Troelsbk/3d-printed-line-follower-robot-stm32/KiCad/KiCad.kicad_sch

## KiCad design KiCad/KiCad.kicad_sch (2025-11-29)

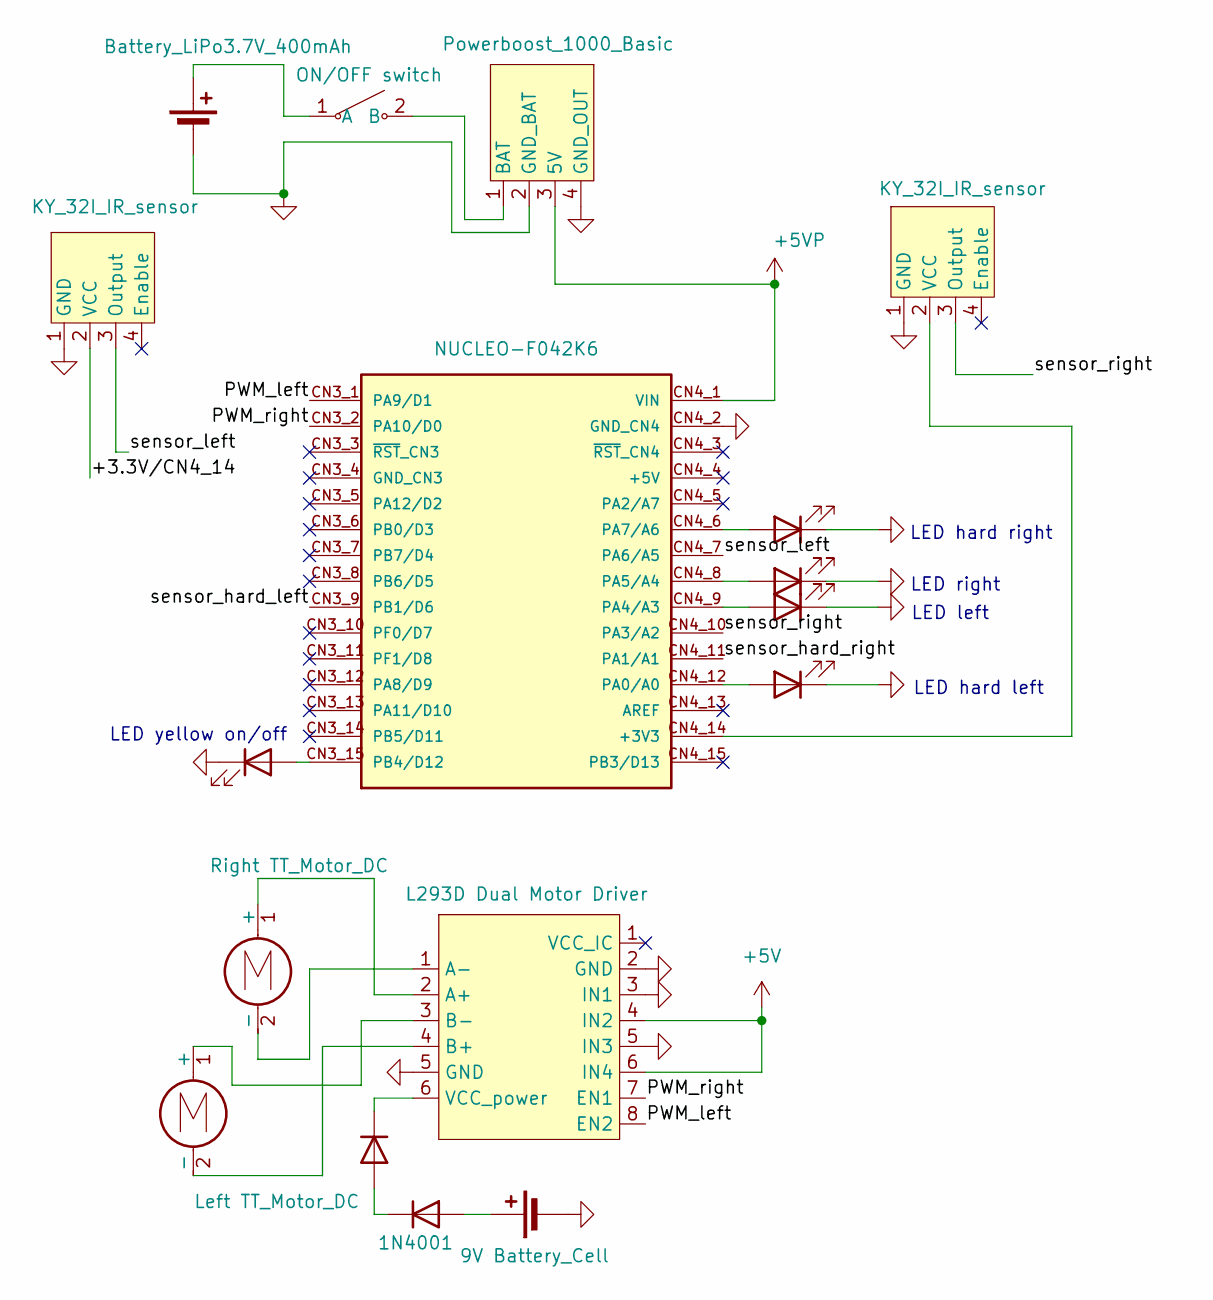
[picture p16: schematic KiCad.kicad_sch]

Parts:
BT1: 9V Battery_Cell
BT2: Battery_LiPo3.7V_400mAh
D1, D2, D3, D4, D7: LED
D5, D6: 1N4001; D_DO-41_SOD81_P10.16mm_Horizontal
M1: Right TT_Motor_DC
M2: Left TT_Motor_DC
U1: NUCLEO-F042K6; MODULE_NUCLEO-F042K6; PARTREV 8
U2, U3: KY_32I_IR_sensor
U4: Powerboost_1000_Basic
U6: ON/OFF switch
U7: L293D Dual Motor Driver

Connections:
+3.3V/CN4_14: U2.2 (VCC)
+5V: U7.4 (B+), U7.6 (VCC_power)
+5VP: U1.CN4_1 (VIN), U4.3 (5V)
GND: BT1.2 (-), BT2.2 (-), D1.1 (K), D2.1 (K), D3.1 (K), D4.1 (K), D7.1 (K), U1.CN4_2 (GND_CN4), U2.1 (GND), U3.1 (GND), U4.2 (GND_BAT), U4.4 (GND_OUT), U7.2 (A+), U7.3 (B-), U7.5 (GND)
unnamed: BT1.1 (+), D5.2 (A)
unnamed: BT2.1 (+), U6.1 (A)
unnamed: D1.2 (A), U1.CN4_12 (PA0/A0)
unnamed: D2.2 (A), U1.CN4_6 (PA7/A6)
unnamed: D3.2 (A), U1.CN4_9 (PA4/A3)
unnamed: D4.2 (A), U1.CN4_8 (PA5/A4)
unnamed: D5.1 (K), D6.2 (A)
unnamed: D6.1 (K), U7.6 (VCC_power)
unnamed: D7.2 (A), U1.CN3_15 (PB4/D12)
unnamed: M1.1 (+), U7.2 (A+)
unnamed: M1.2 (-), U7.1 (A-)
unnamed: M2.1 (+), U7.3 (B-)
unnamed: M2.2 (-), U7.4 (B+)
unnamed: U1.CN4_14 (+3V3), U3.2 (VCC)
unnamed: U4.1 (BAT), U6.2 (B)
PWM_left: U1.CN3_1 (PA9/D1), U7.8 (EN2)
PWM_right: U1.CN3_2 (PA10/D0), U7.7 (EN1)
sensor_hard_left: U1.CN3_9 (PB1/D6)
sensor_hard_right: U1.CN4_11 (PA1/A1)
sensor_left: U1.CN4_7 (PA6/A5), U2.3 (Output)
sensor_right: U1.CN4_10 (PA3/A2), U3.3 (Output)

Notes on the sheet:
LED right
LED yellow on/off
LED hard left
LED hard right
LED left
